Fermium/ltk-mw-mechanics/3DP Platters/OLD/ltk-mw_device_fulcrum_0.3mm_PLA_MK3.3mf

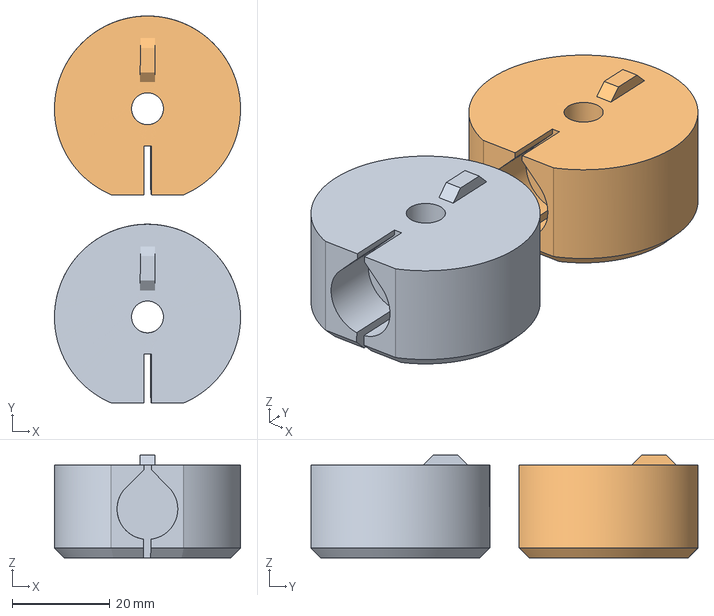
[picture p30: CAD file, 2019-07-17, an earlier design]
3DP Platters/OLD/ltk-mw_device_fulcrum_0.3mm_PLA_MK3.3mf
38.0 x 79.0 x 21.0 mm
