Fermium/ltk-mw-mechanics/3DP Platters/OLD/ltk-mw_sliders_0.3mm_PLA_MK3.3mf

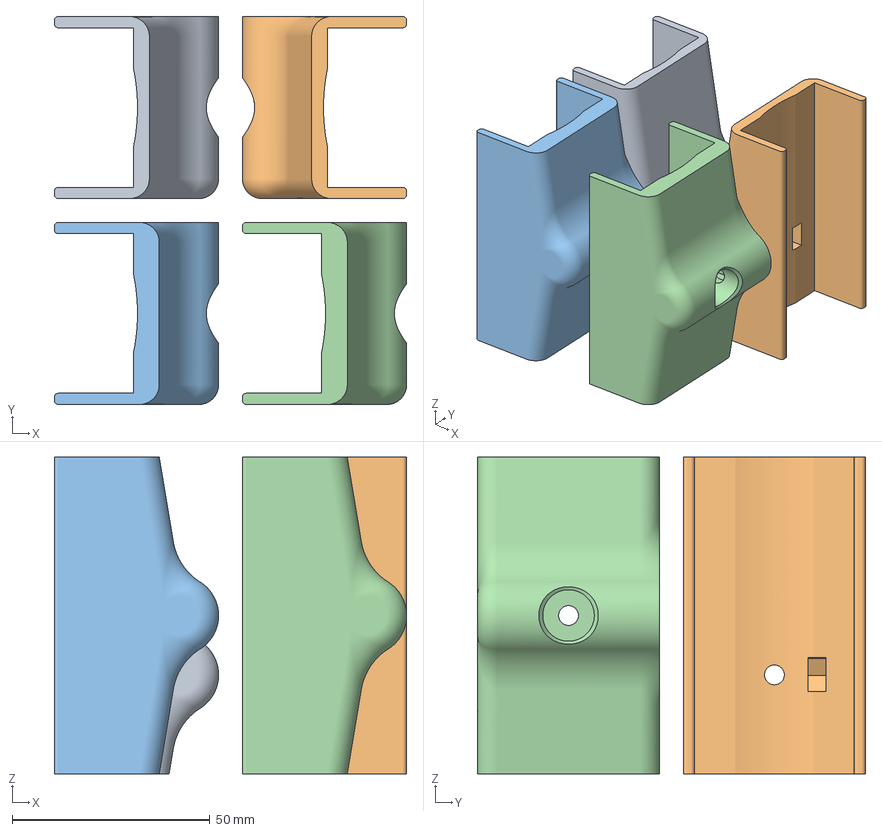
[picture p31: CAD file, 2019-07-17, an earlier design]
3DP Platters/OLD/ltk-mw_sliders_0.3mm_PLA_MK3.3mf
89.0 x 98.0 x 80.0 mm
