Fermium/ltk-mw-mechanics/3DP Platters/OLD/ltk-mw_foot_3dp_0.3mm_PLA_MK3.3mf

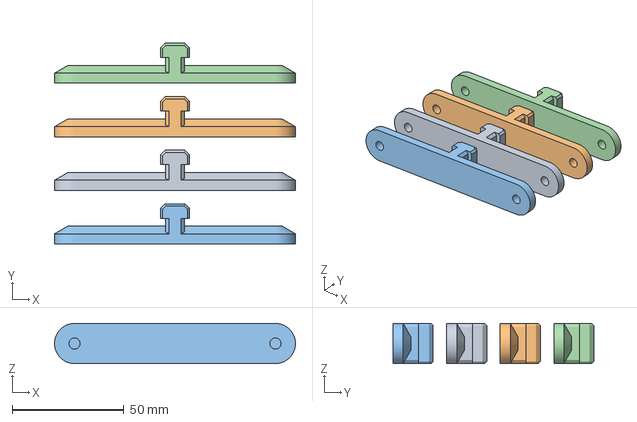
[picture p32: CAD file, 2019-07-17, an earlier design]
3DP Platters/OLD/ltk-mw_foot_3dp_0.3mm_PLA_MK3.3mf
108.0 x 90.0 x 18.0 mm
