Fermium/ltk-mw-mechanics/3DP Platters/OLD/ltk-mw_vice_3dp_0.3mm_PLA_MK3.3mf

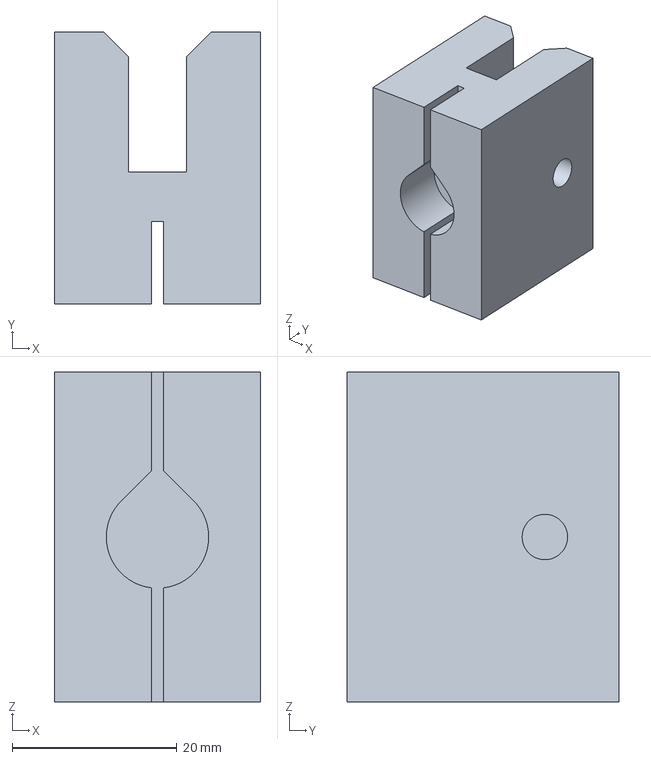
[picture p33: CAD file, 2019-07-17, an earlier design]
3DP Platters/OLD/ltk-mw_vice_3dp_0.3mm_PLA_MK3.3mf
25.0 x 33.0 x 40.0 mm
