Fermium/ltk-mw-mechanics/pcbs/exports/center_index/center_index.PDF

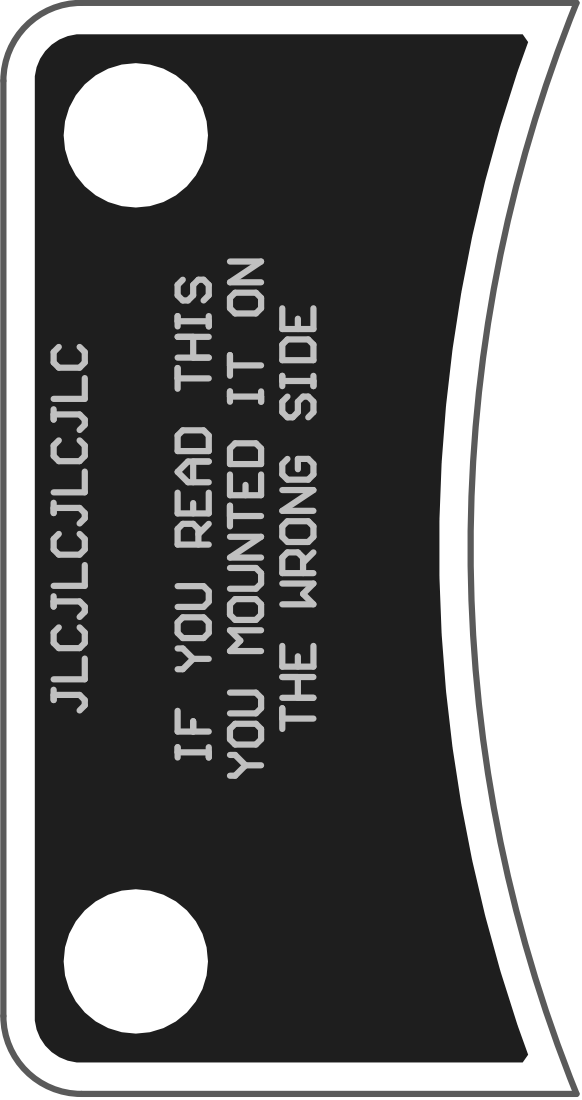
[picture p37: page 1]
