Fermium/ltk-mw-mechanics/pcbs/exports/center_protractor/center_protractor.PDF

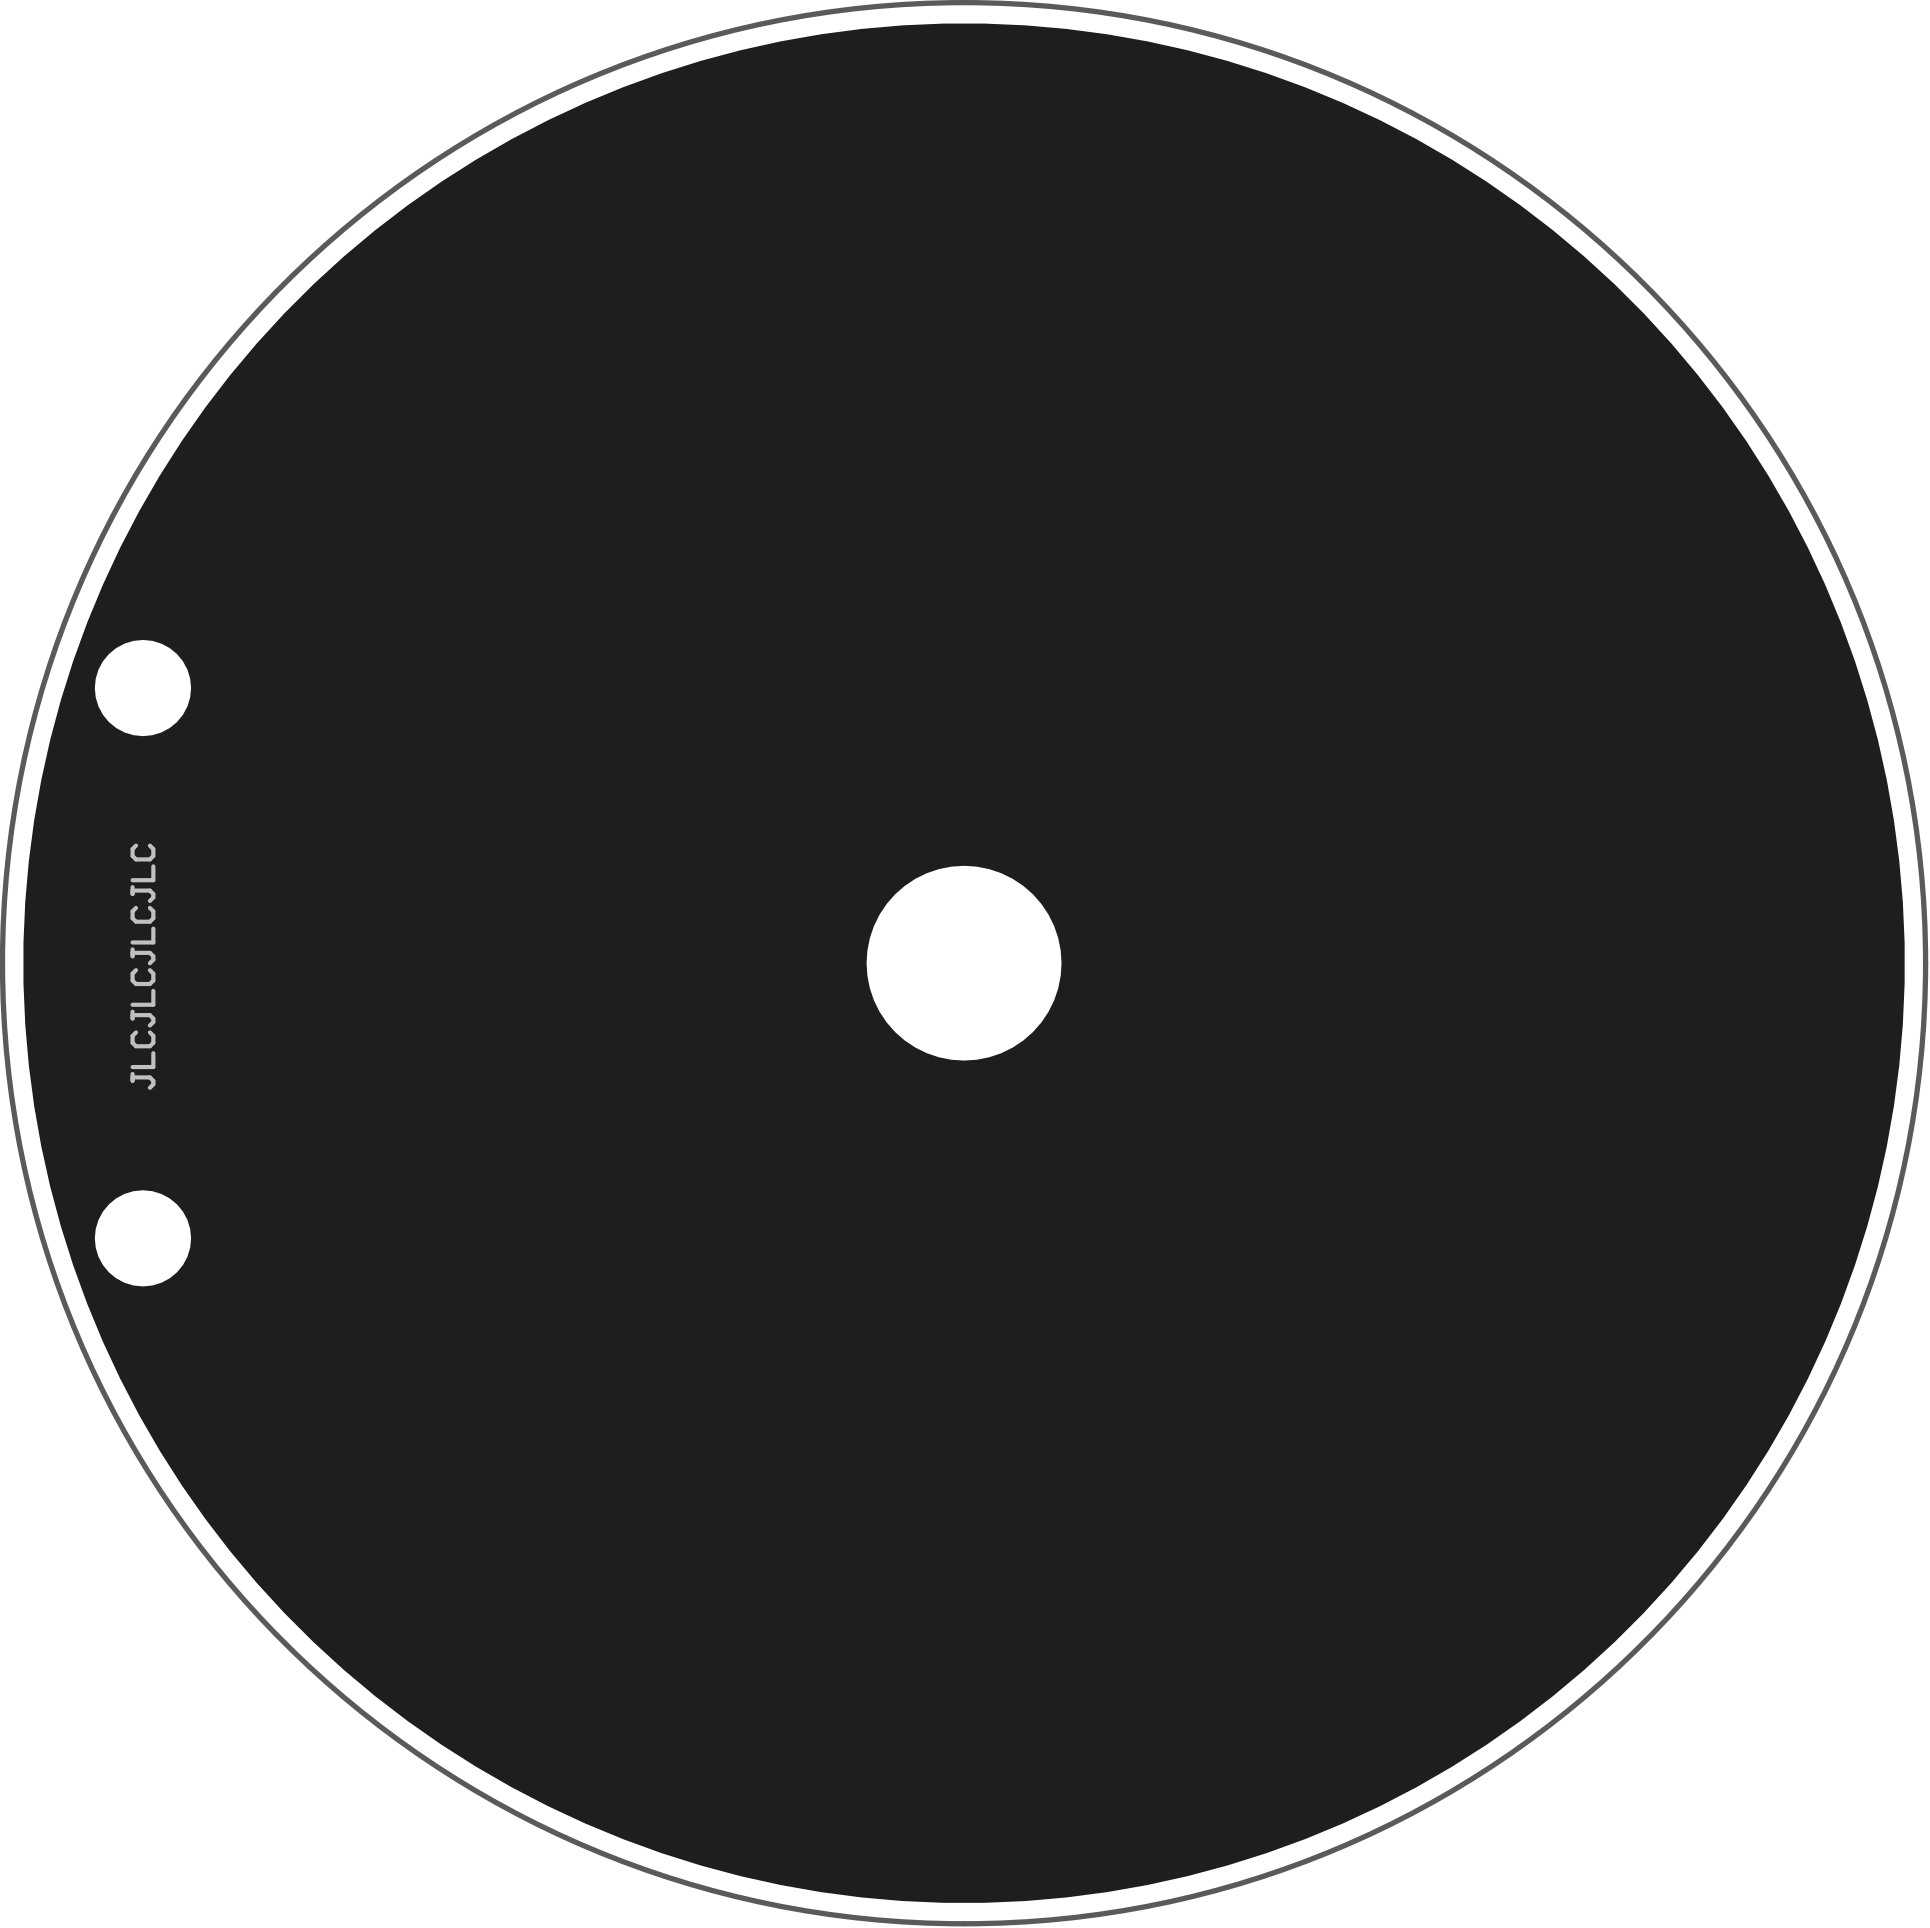
[picture p38: page 1]
