Fermium/ltk-mw-mechanics/pcbs/exports/device_index/device_index.PDF

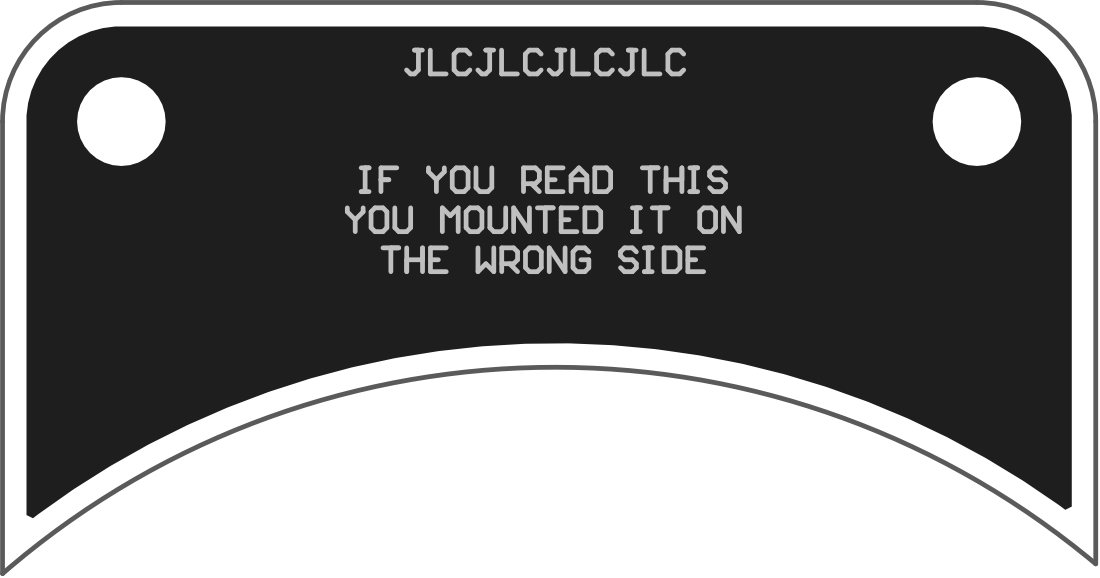
[picture p39: page 1]
