Fermium/ltk-mw-mechanics/pcbs/exports/device_protractor/device_protractor.PDF

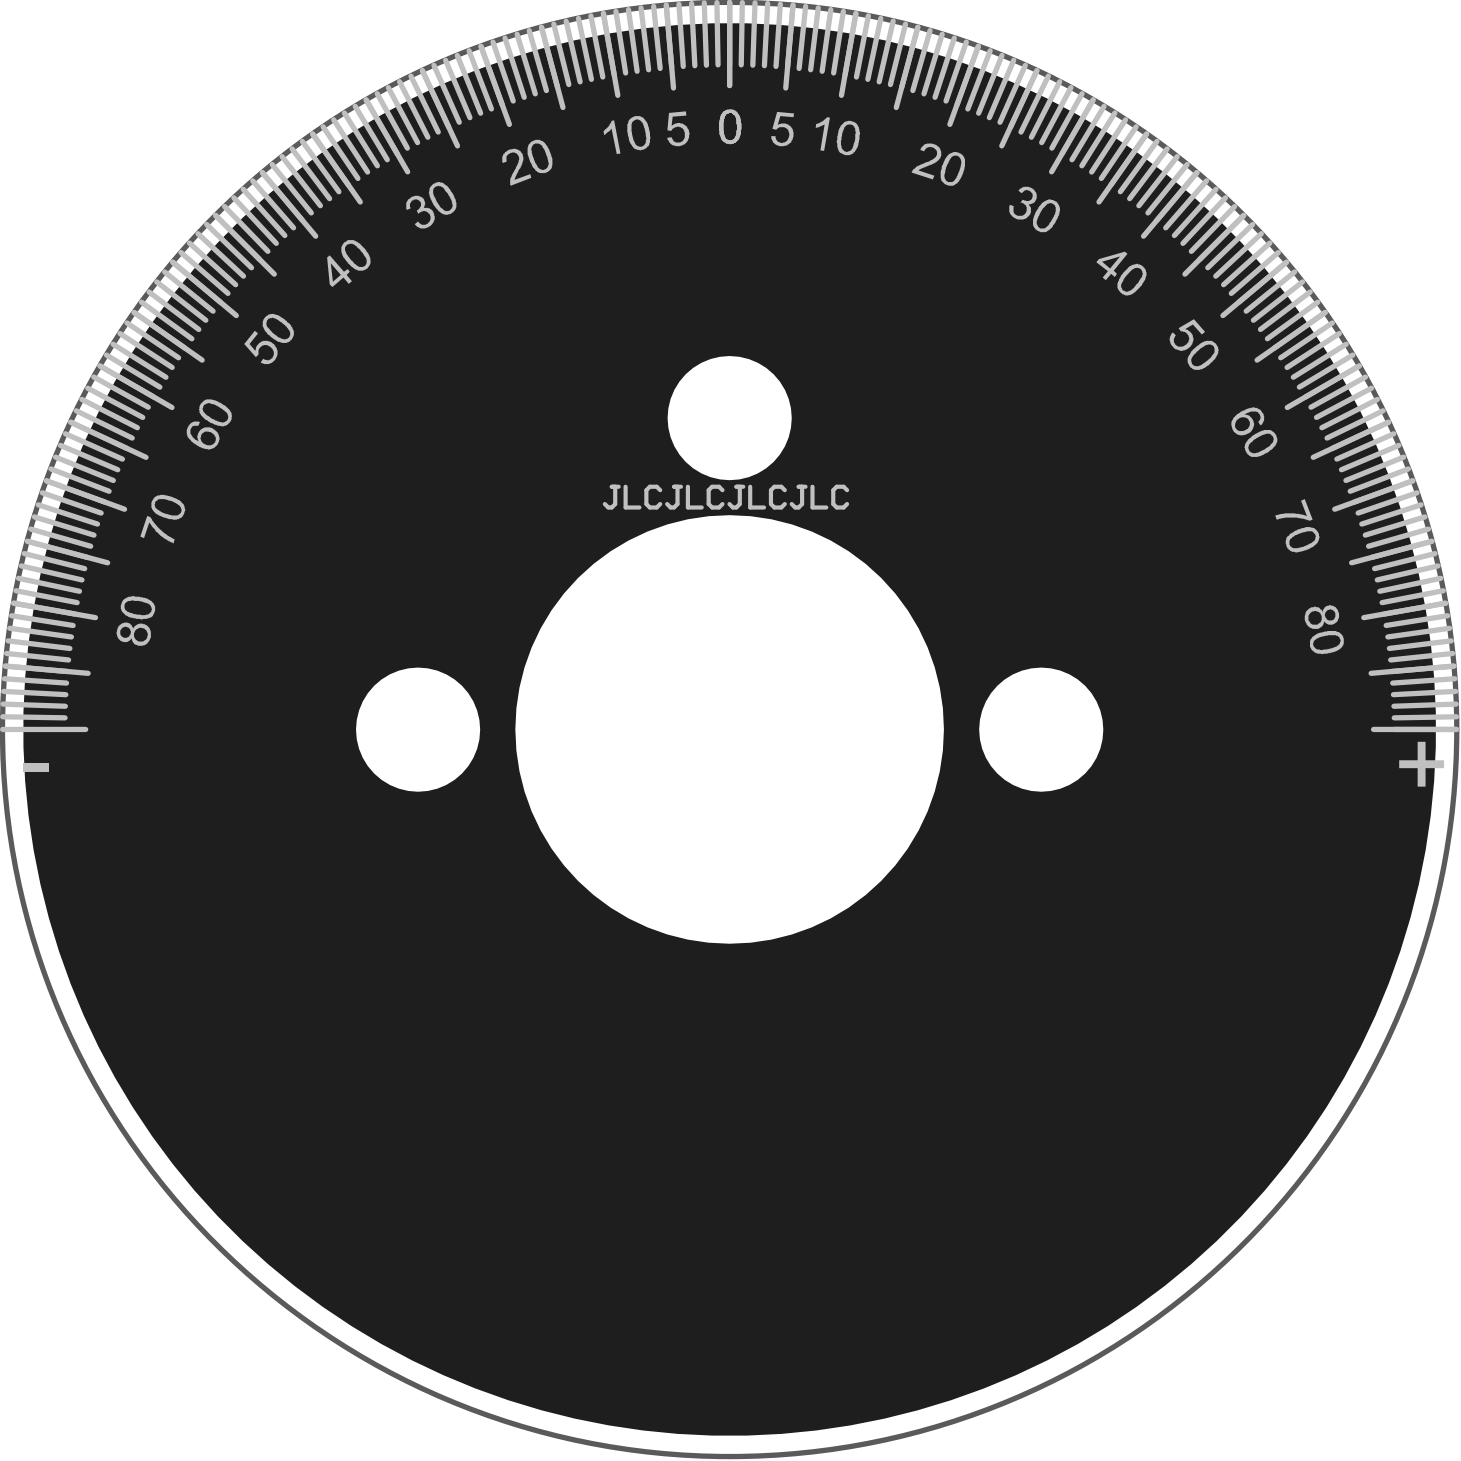
[picture p40: page 1]
