Fermium/ltk-mw-mechanics/pcbs/exports/double_slot/double_slot.PDF

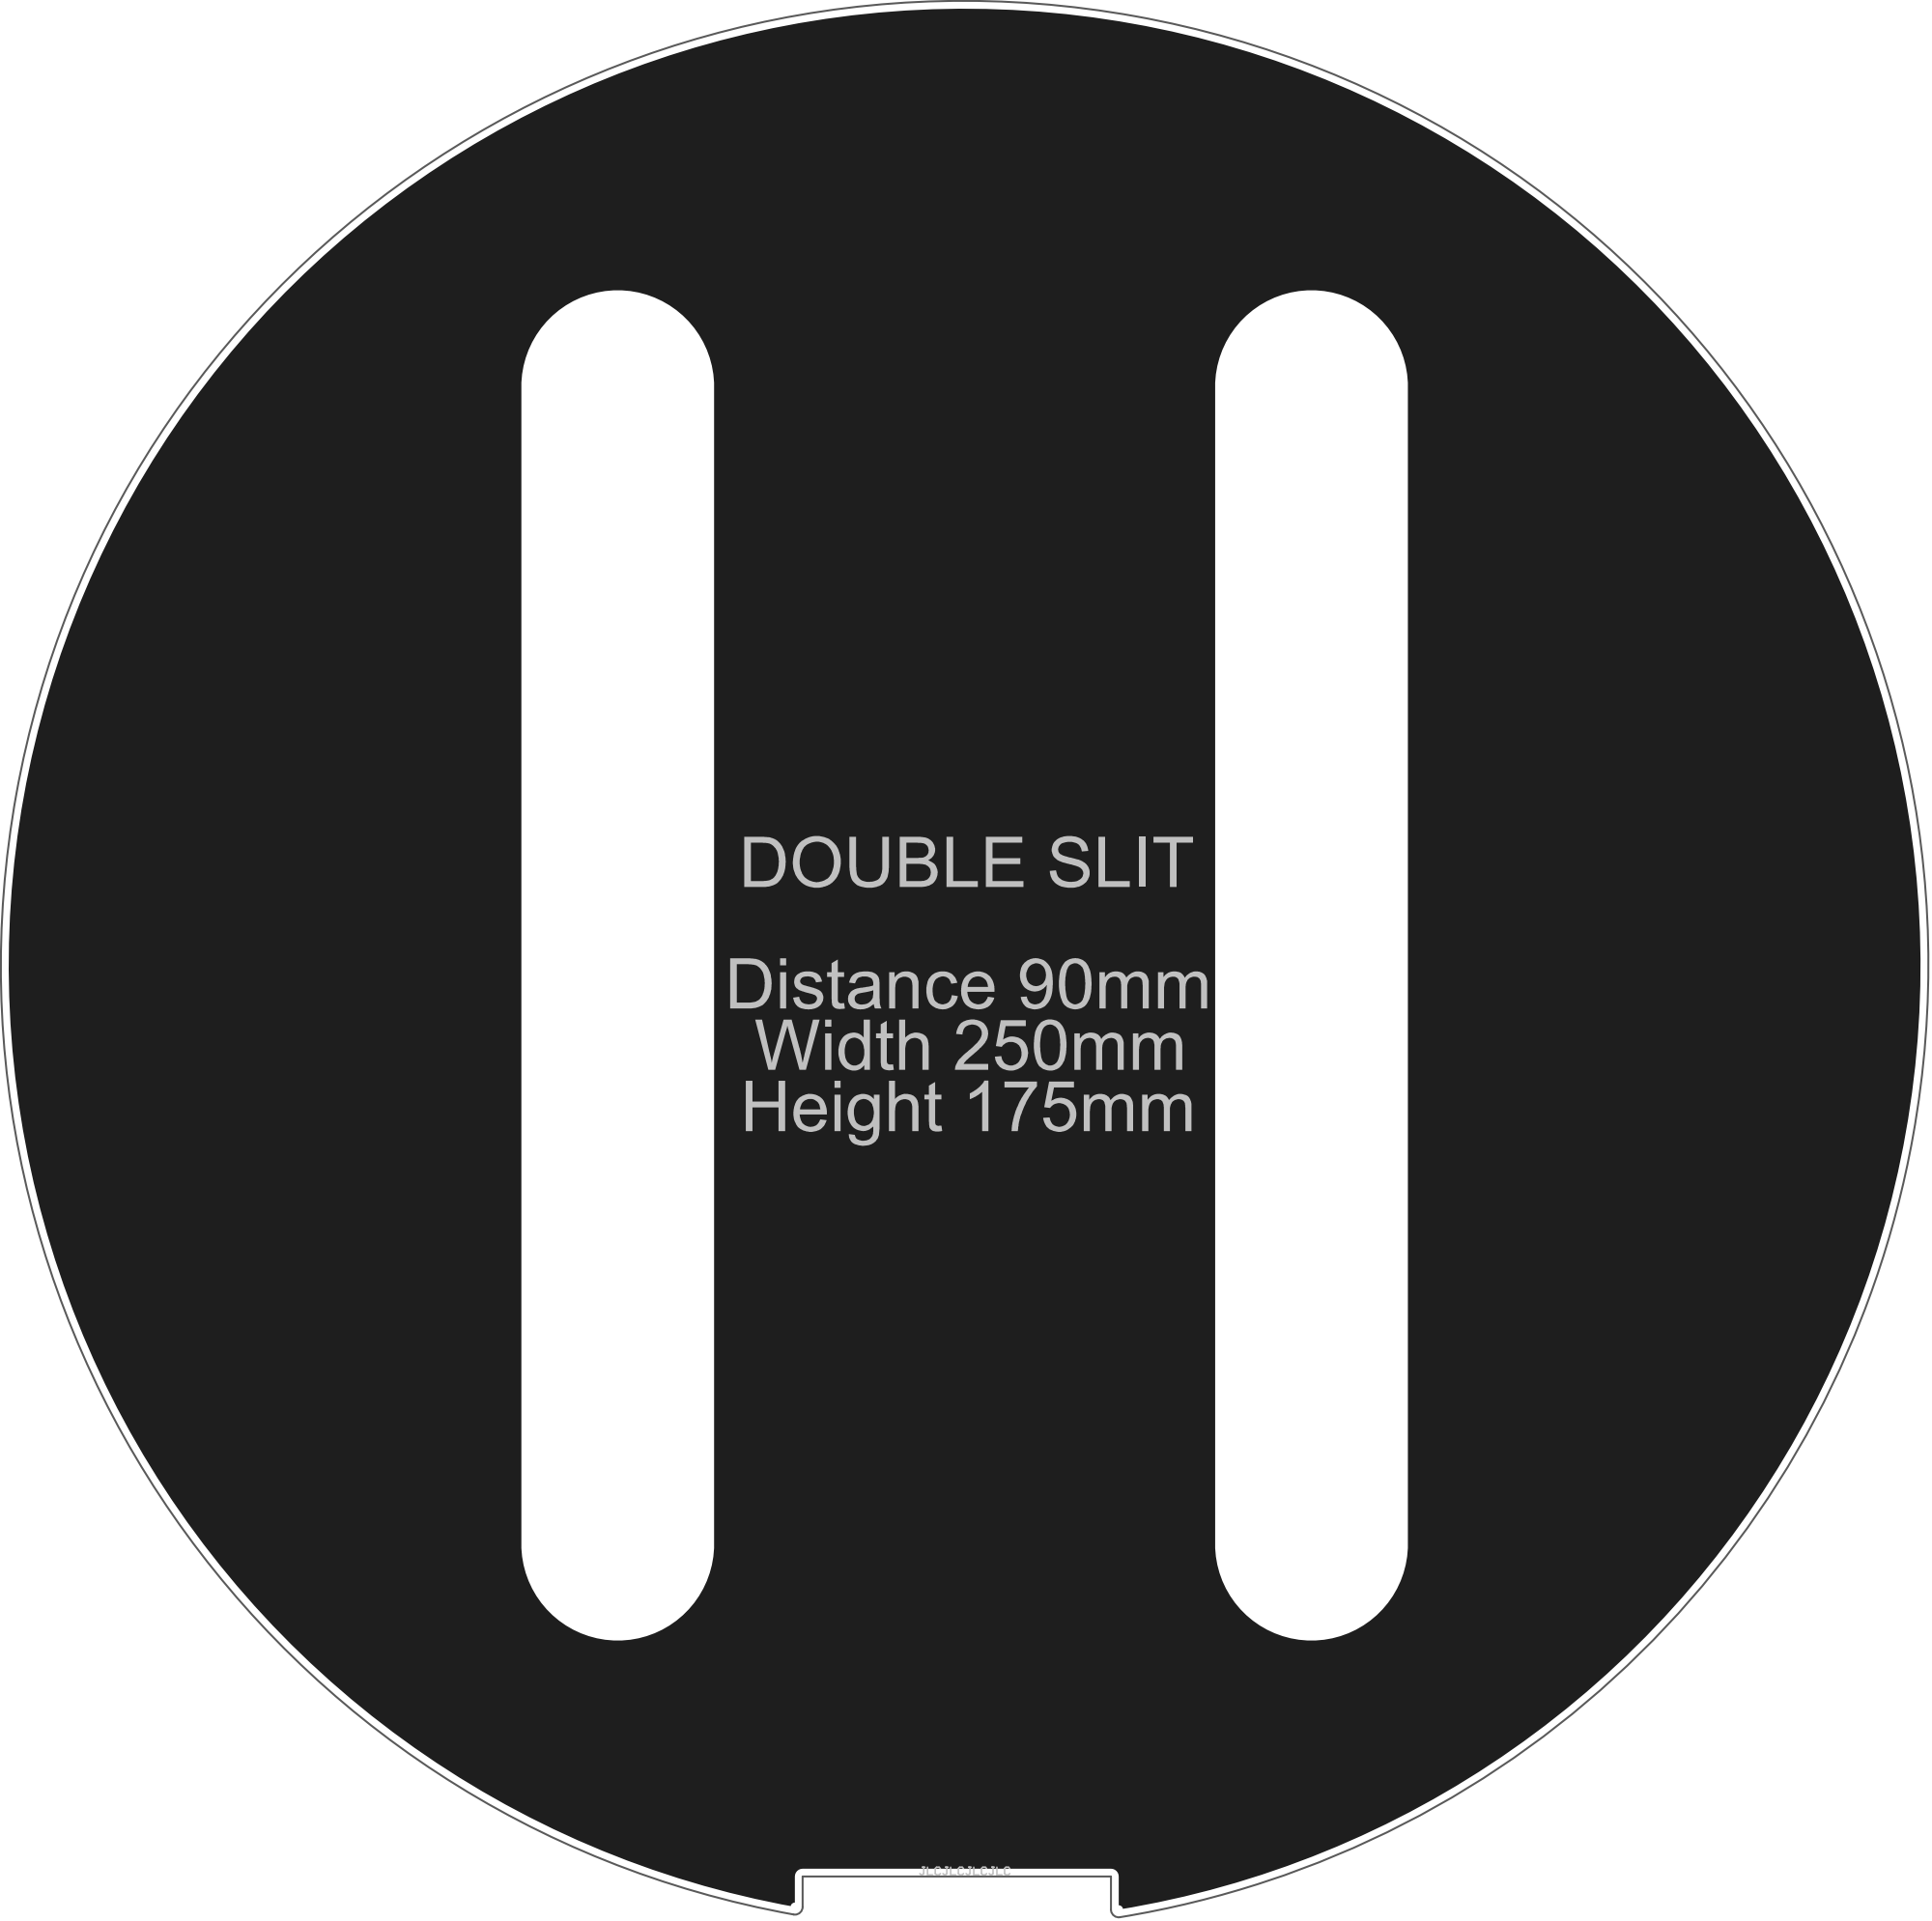
[picture p41: page 1]
