Fermium/ltk-mw-mechanics/pcbs/exports/fresnel_plates/fresnel_plates.PDF

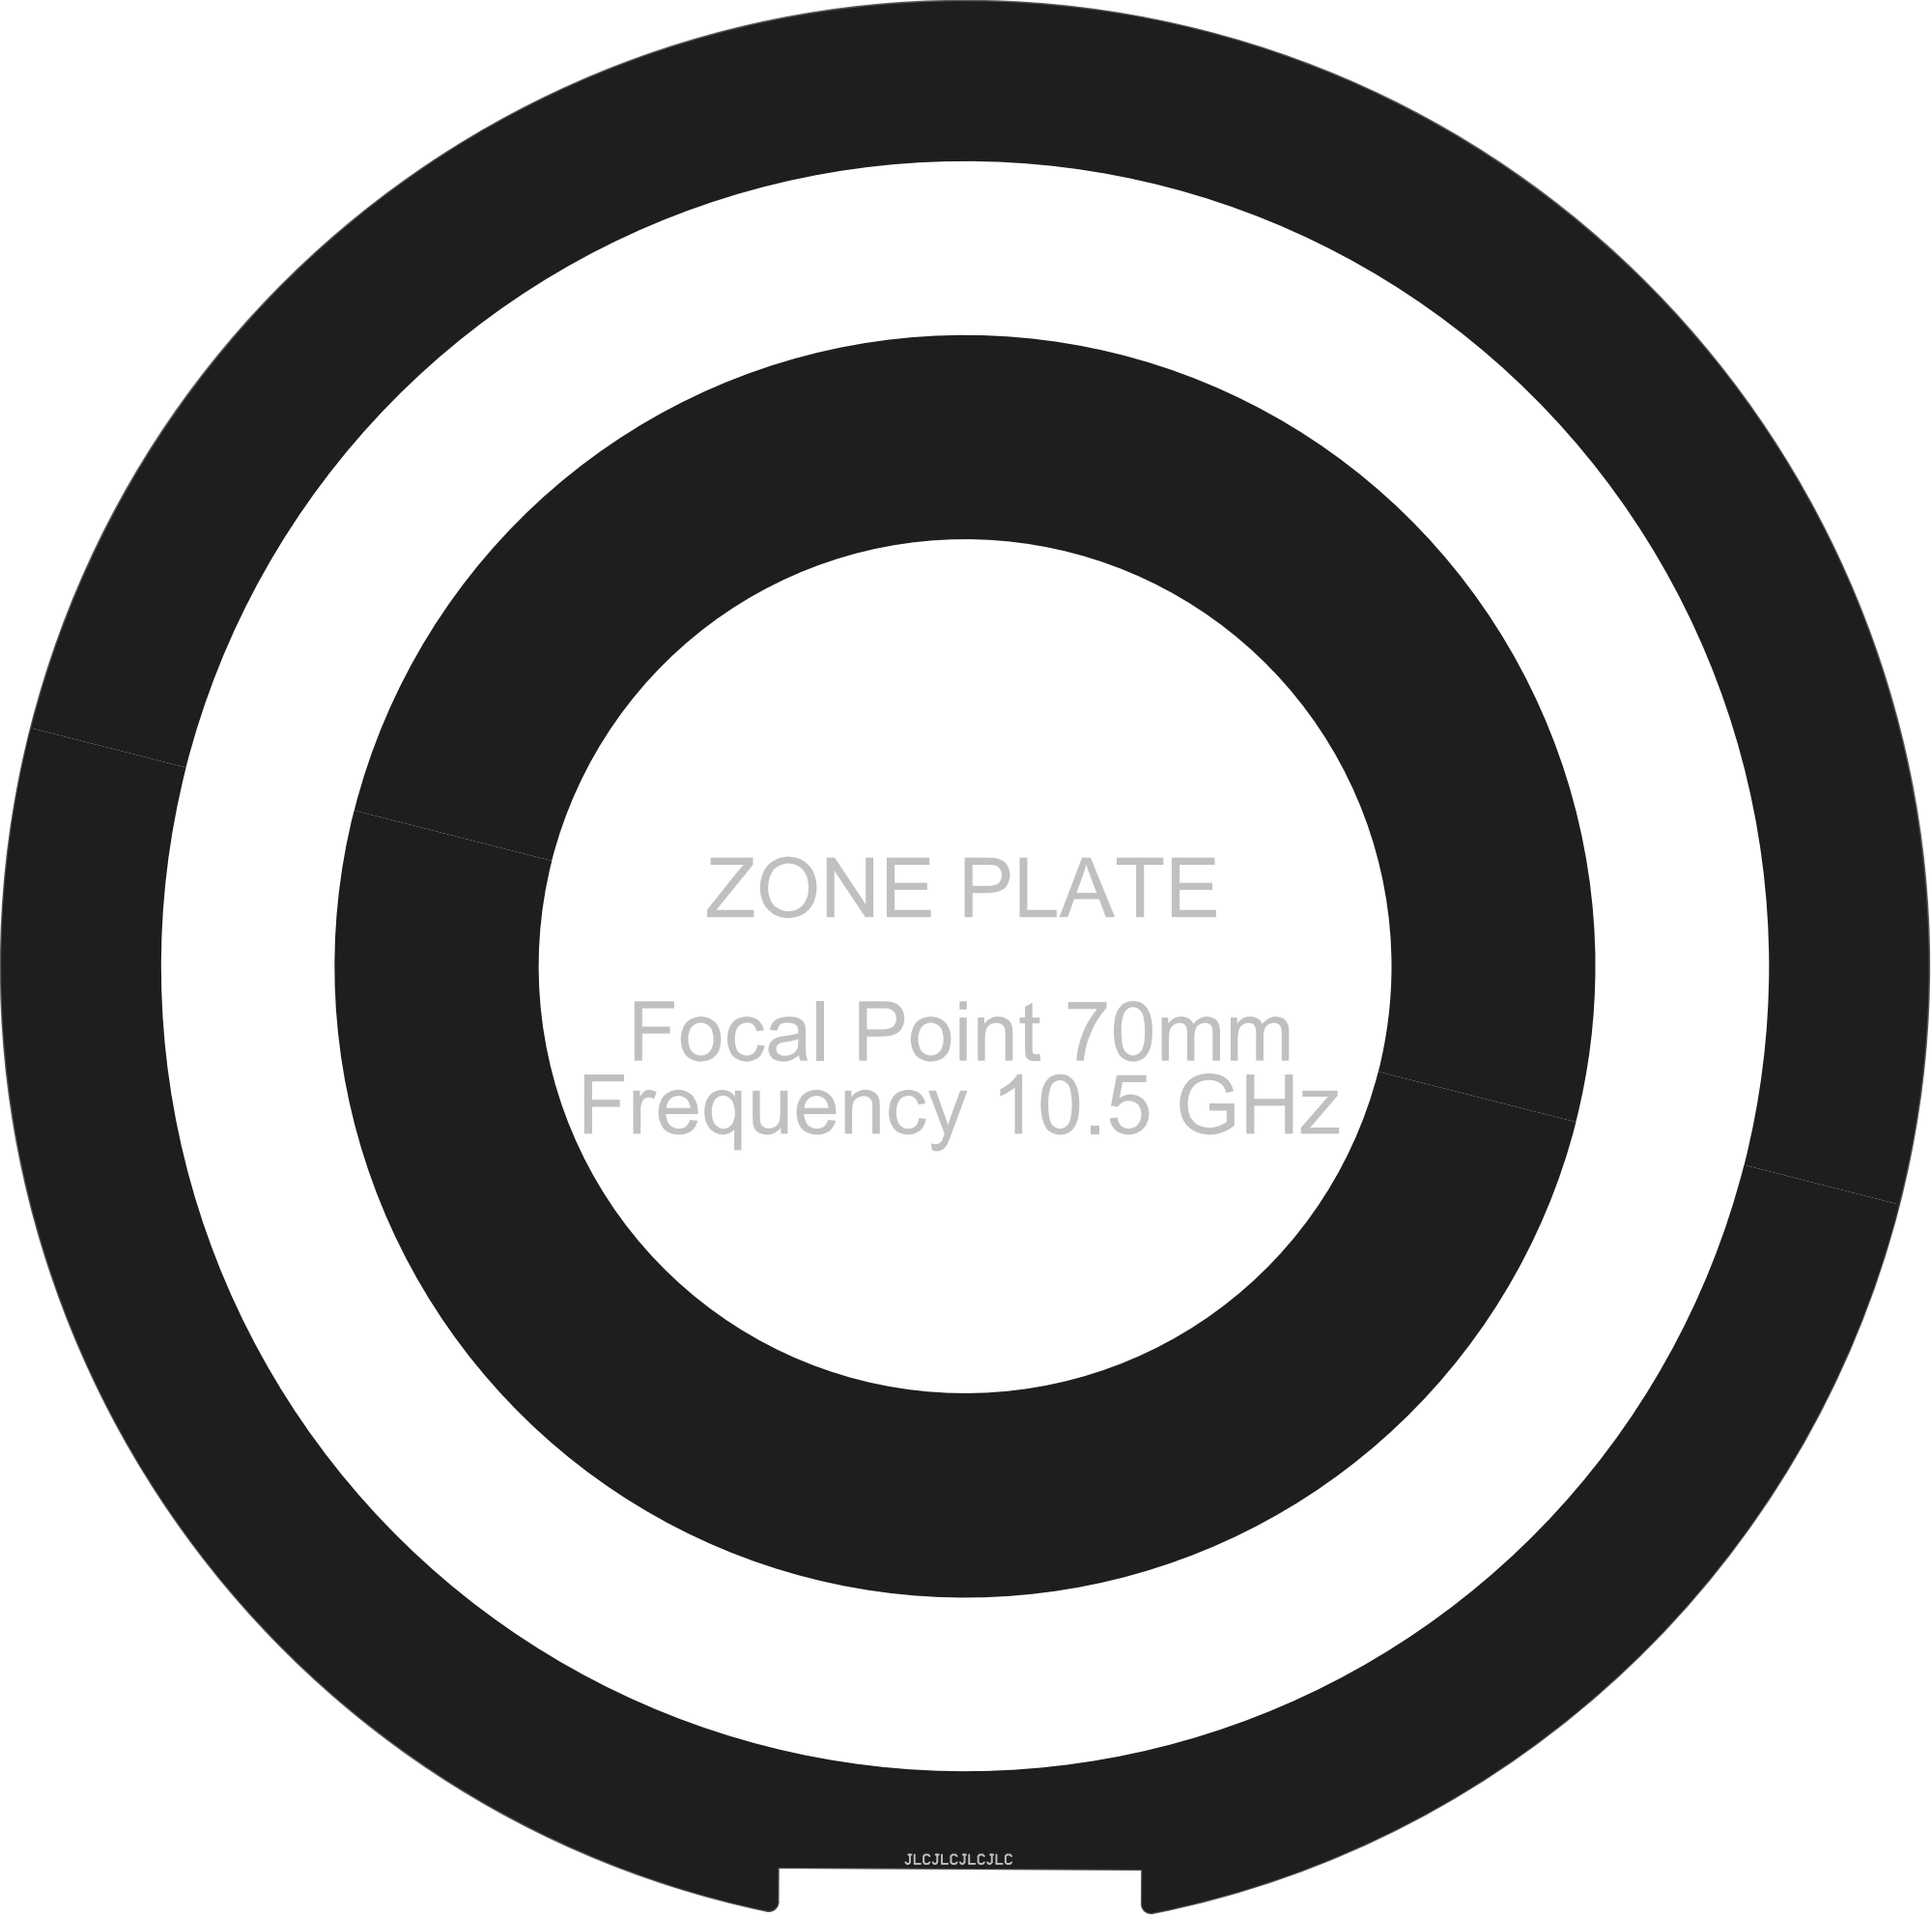
[picture p42: page 1]
