Fermium/ltk-mw-mechanics/pcbs/exports/mirror/mirror.PDF

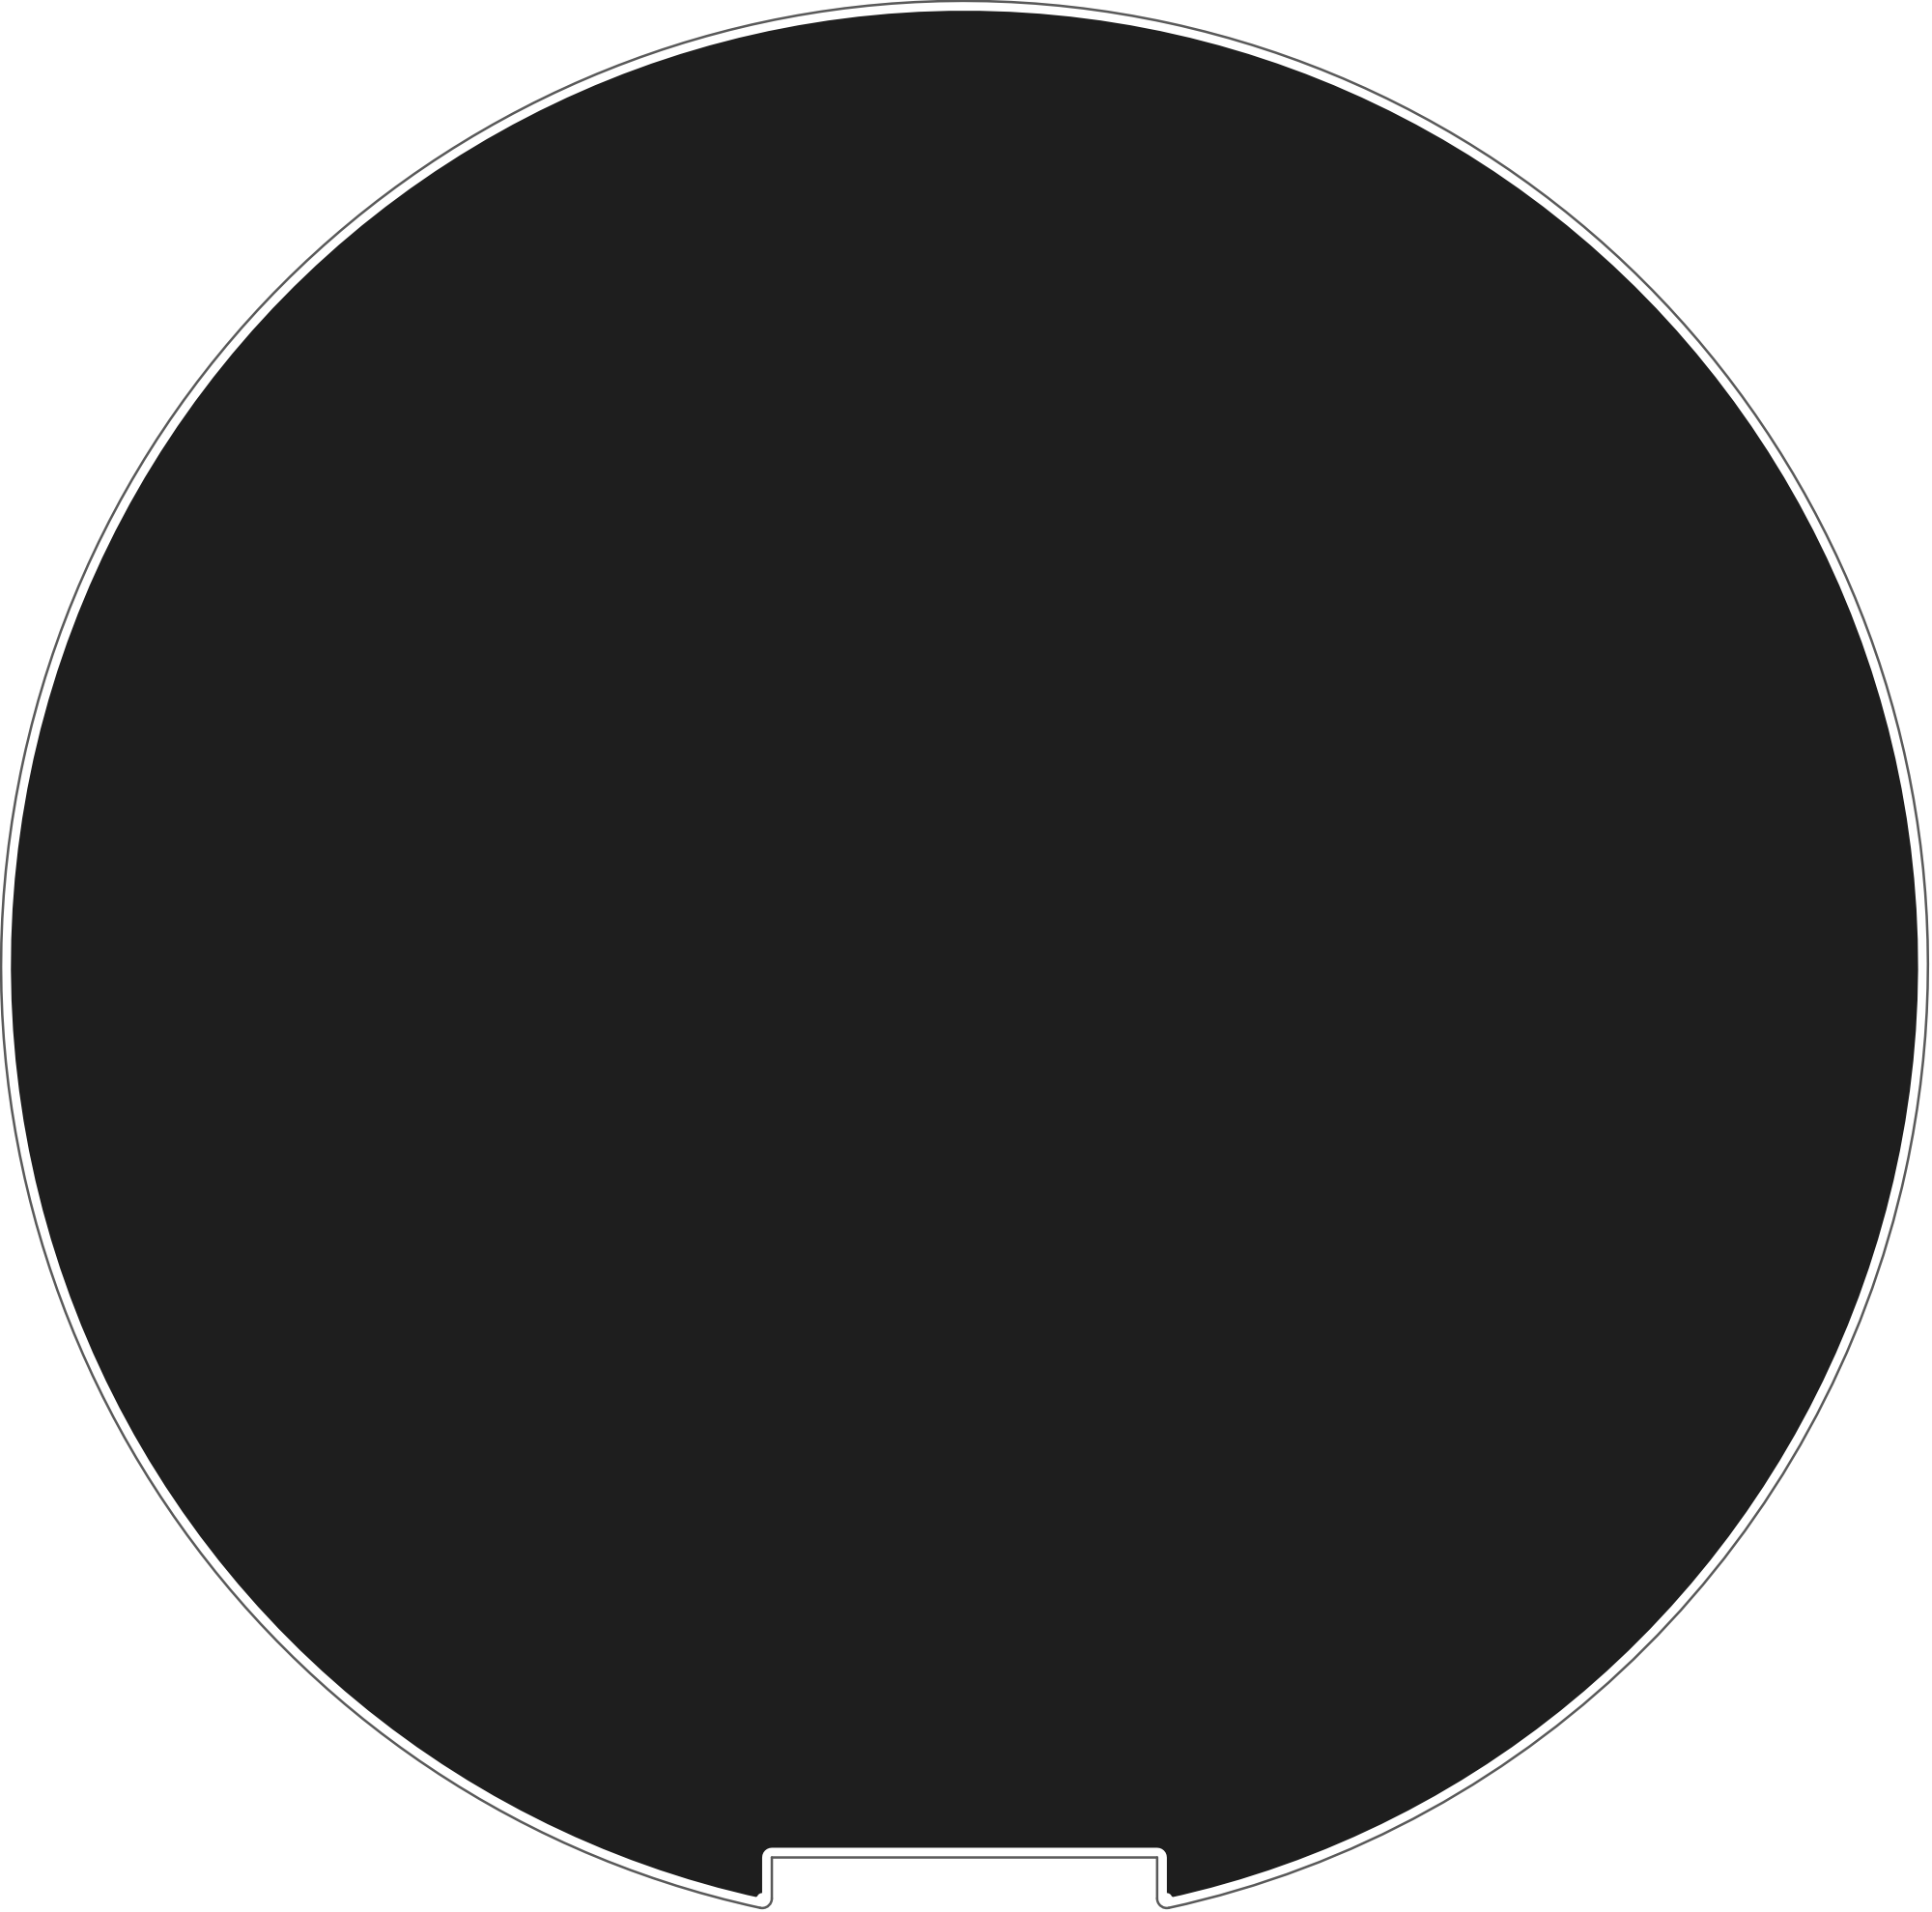
[picture p43: page 1]
