Fermium/ltk-mw-mechanics/pcbs/exports/photon_sieve/photon_sieve.PDF

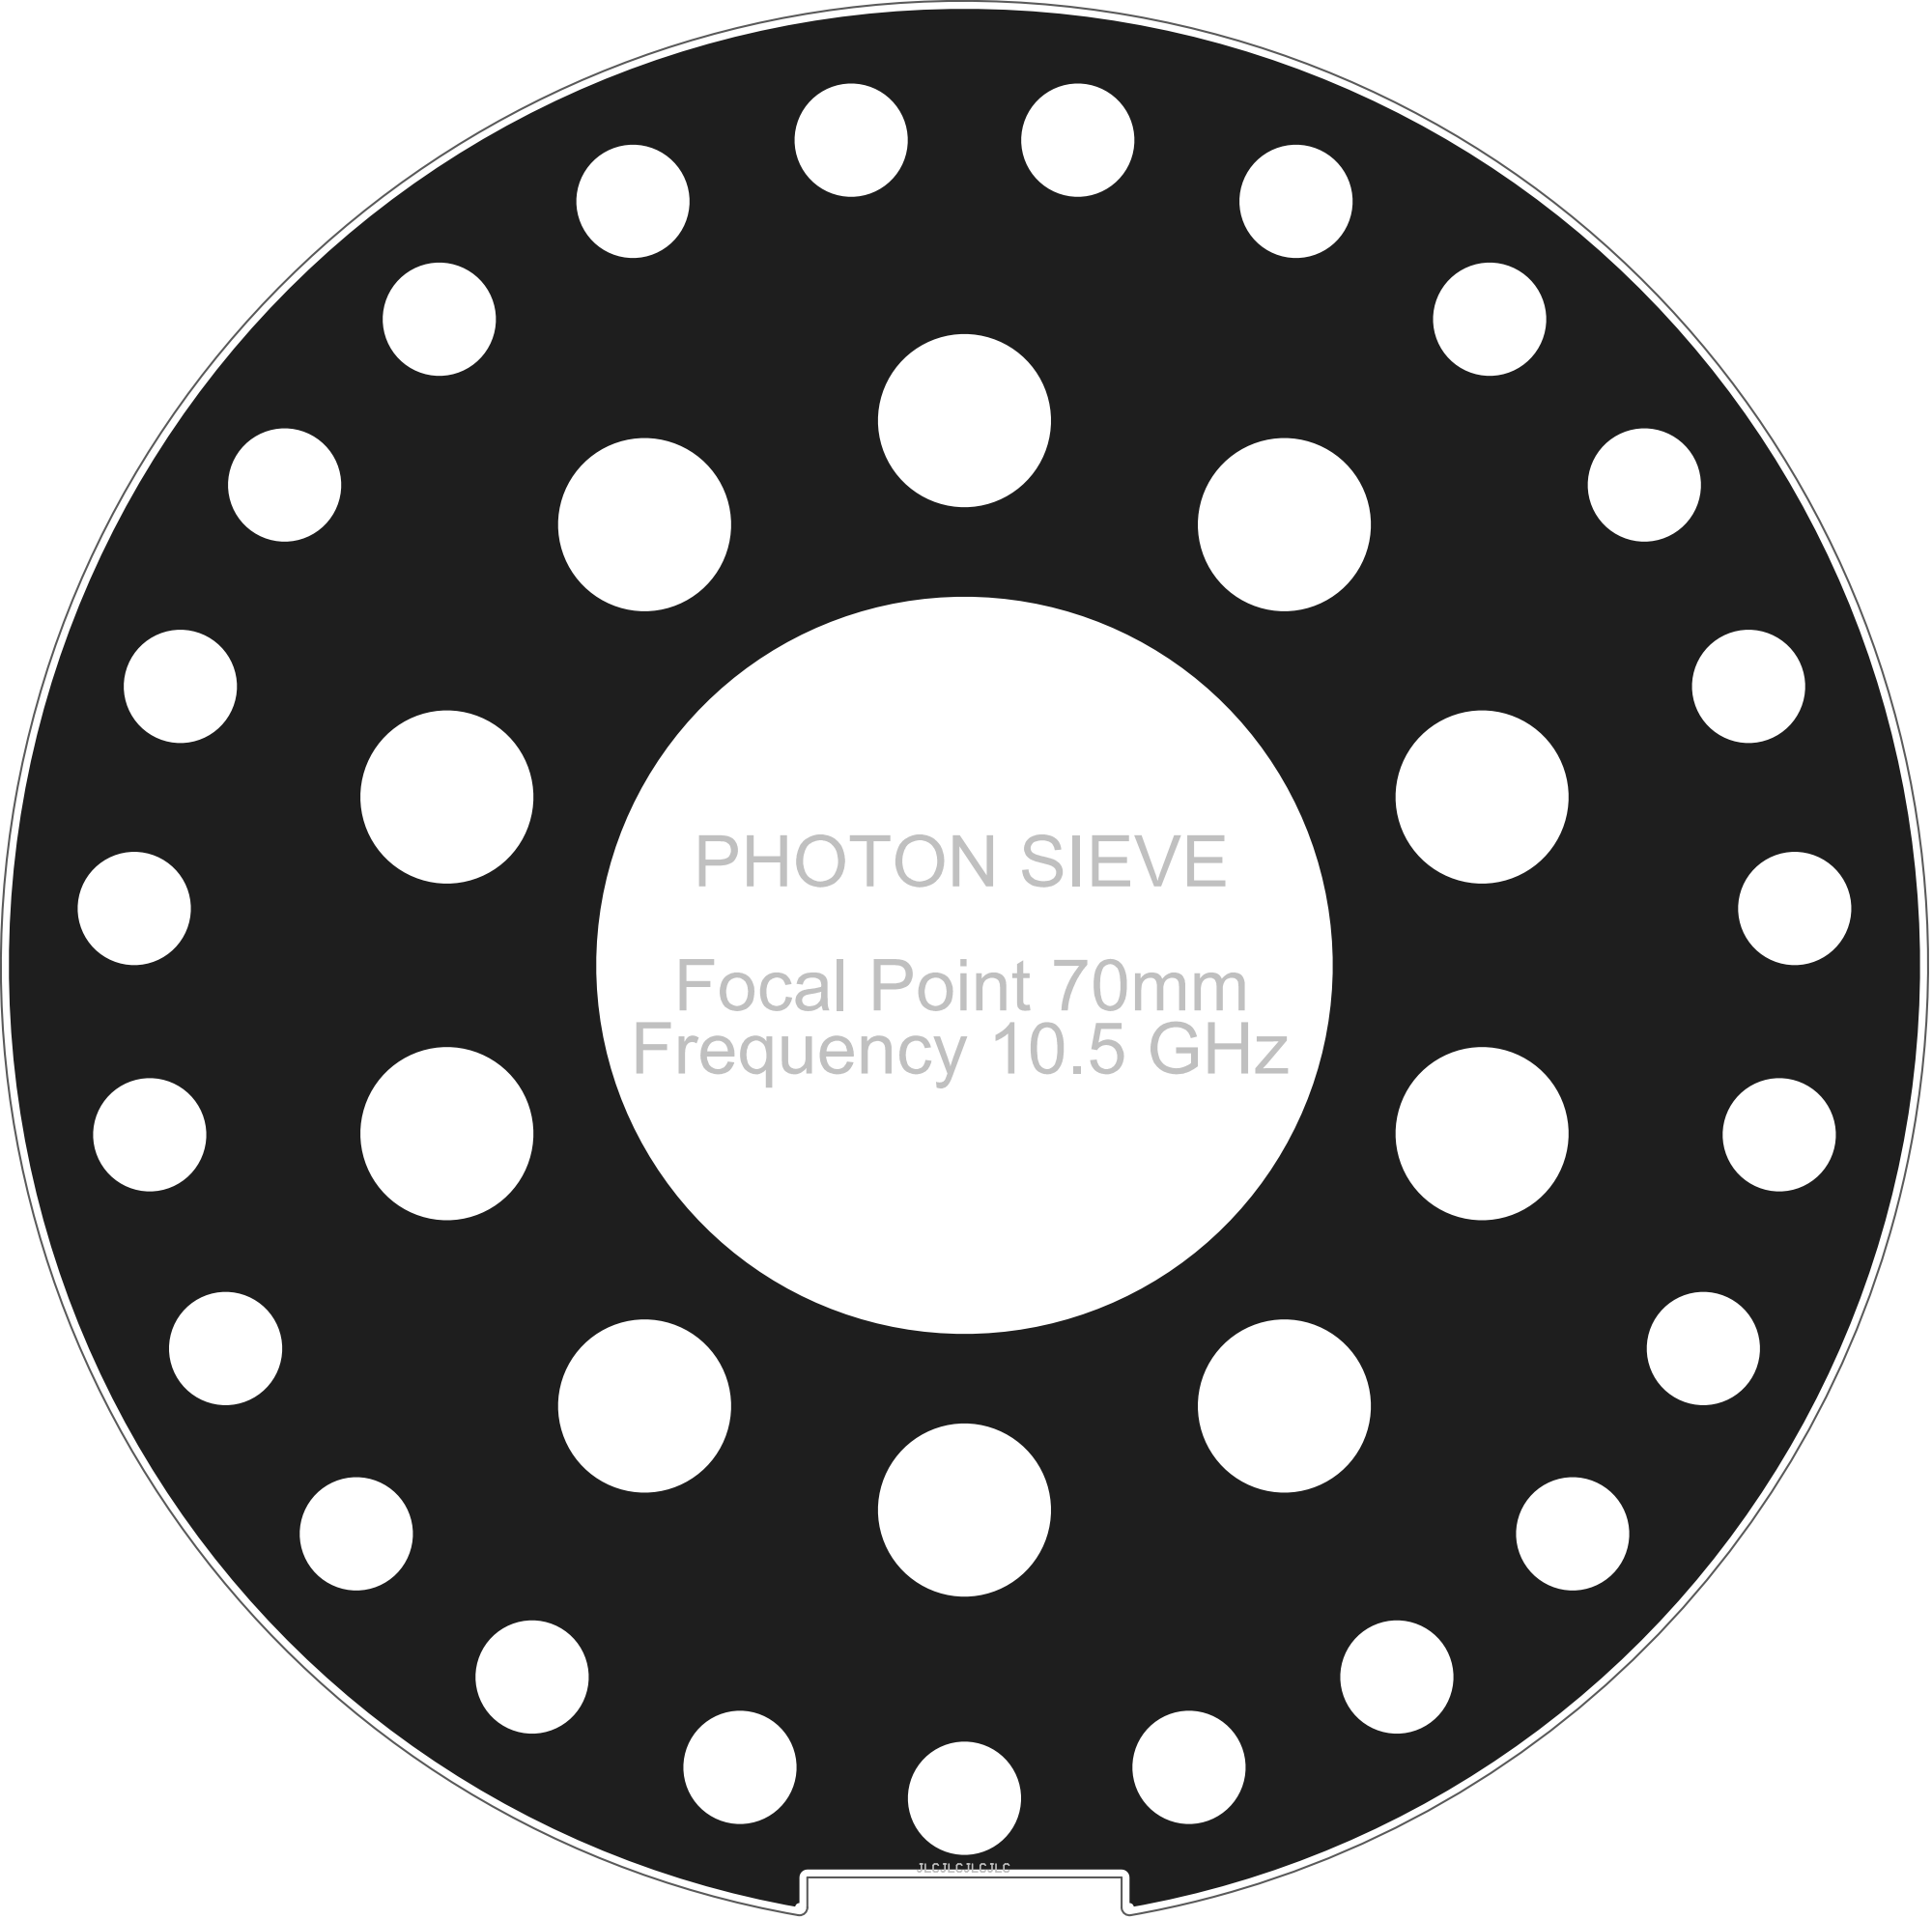
[picture p44: page 1]
