Fermium/ltk-mw-mechanics/pcbs/exports/polarizer/polarizer.PDF

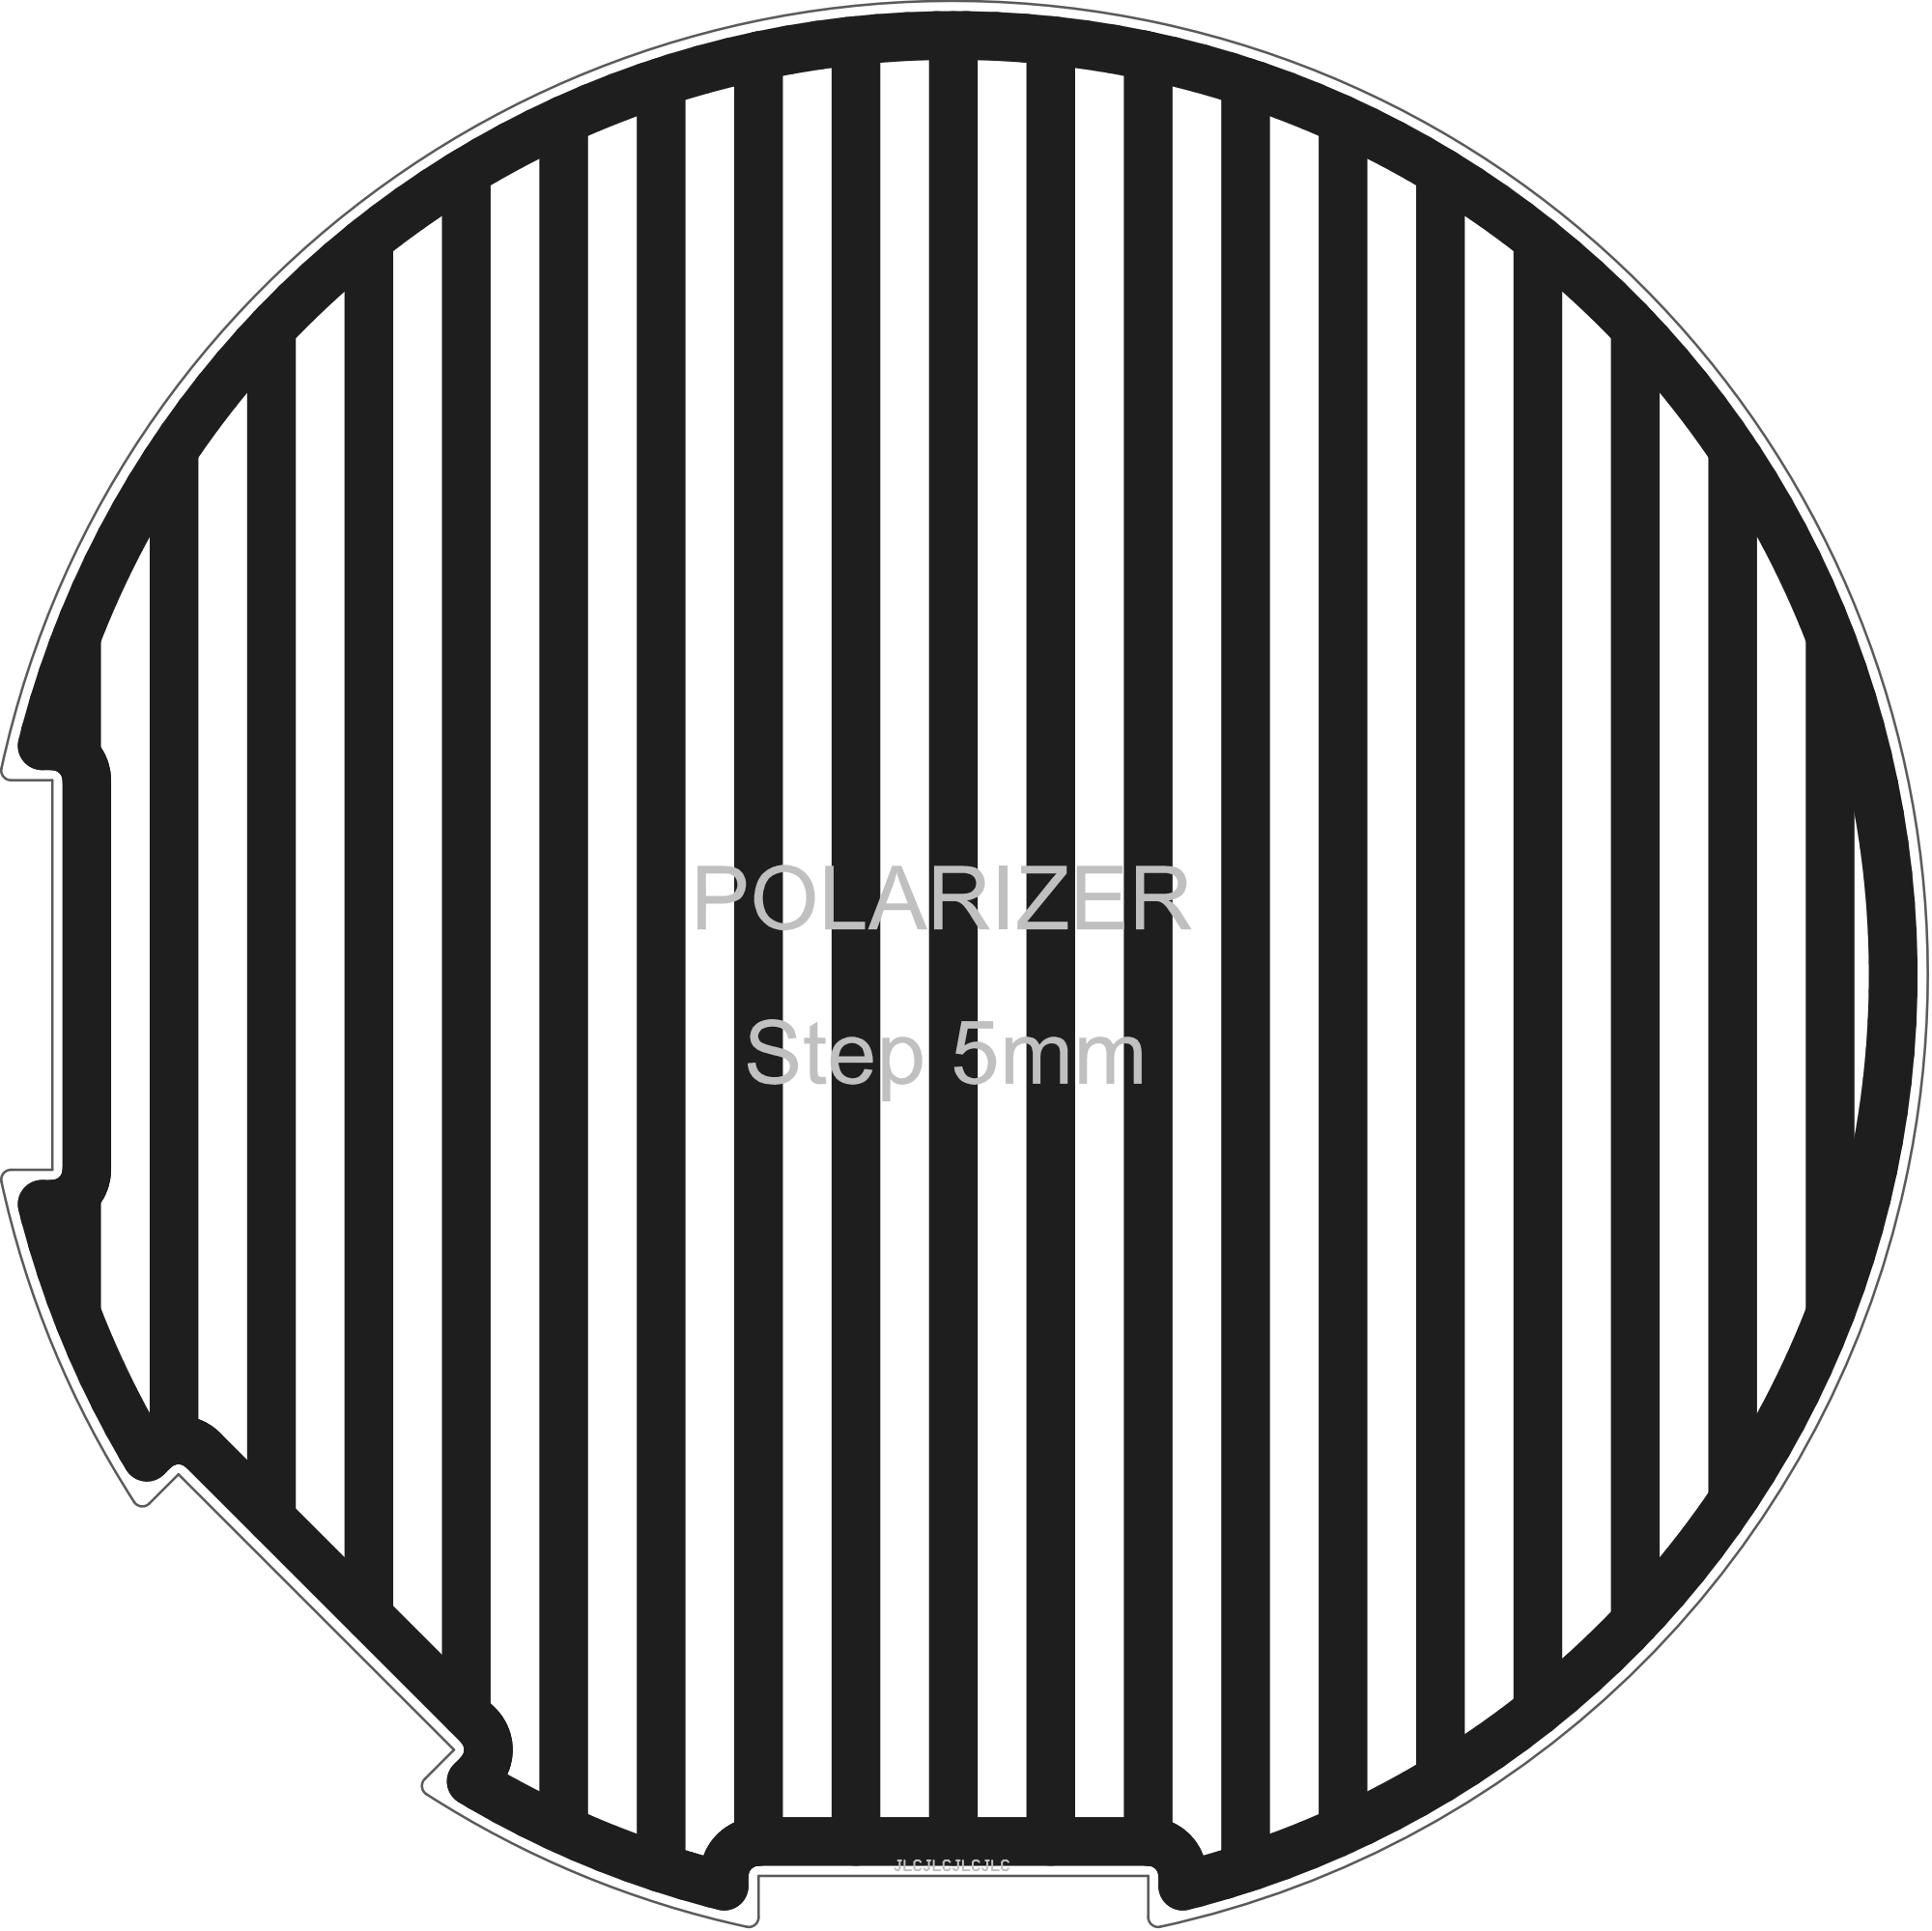
[picture p45: page 1]
